STHQ/kilaueacove/tikinook/neopixel.py

# Adafruit NeoPixel library port to the rpi_ws281x library.
# Author: Tony DiCola (tony@tonydicola.com), Jeremy Garff (jer@jers.net)
import _rpi_ws281x as ws


def Color(red, green, blue):
    """Convert the provided red, green, blue color to a 24-bit color value.
    Each color component should be a value 0-255 where 0 is the lowest intensity
    and 255 is the highest intensity.
    """
    return (red << 16) | (green << 8) | blue


class _LED_Data(object):
    """Wrapper class which makes a SWIG LED color data array look and feel like
    a Python list of integers.
    """

    def __init__(self, channel, size):
        self.size = size
        self.channel = channel

    def __getitem__(self, pos):
        """Return the 24-bit RGB color value at the provided position or slice
        of positions.
        """
        # Handle if a slice of positions are passed in by grabbing all the values
        # and returning them in a list.
        if isinstance(pos, slice):
            return [ws.ws2811_led_get(self.channel, n) for n in range(pos.indices(self.size))]
        # Else assume the passed in value is a number to the position.
        else:
            return ws.ws2811_led_get(self.channel, pos)

    def __setitem__(self, pos, value):
        """Set the 24-bit RGB color value at the provided position or slice of
        positions.
        """
        # debug
        # print("pos: {}, value: {}", pos, value)
        # Handle if a slice of positions are passed in by setting the appropriate
        # LED data values to the provided values.
        if isinstance(pos, slice):
            index = 0
            for n in range(pos.indices(self.size)):
                ws.ws2811_led_set(self.channel, n, value[index])
                index += 1
        # Else assume the passed in value is a number to the position.
        else:
            # print("pos: {}, value: {}", type(pos), type(value))
            return ws.ws2811_led_set(self.channel, pos, value)
            # Testing value types:
            # print("type value.item(): {}", type(value.item()))
            # return ws.ws2811_led_set(self.channel, pos.item(), value.item())


class Adafruit_NeoPixel(object):
    def __init__(self, num, pin, freq_hz=800000, dma=5, invert=False, brightness=255, channel=0):
        """Class to represent a NeoPixel/WS281x LED display.  Num should be the
        number of pixels in the display, and pin should be the GPIO pin connected
        to the display signal line (must be a PWM pin like 18!).  Optional
        parameters are freq, the frequency of the display signal in hertz (default
        800khz), dma, the DMA channel to use (default 5), invert, a boolean
        specifying if the signal line should be inverted (default False), and
        channel, the PWM channel to use (defaults to 0).
        """
        # Create ws2811_t structure and fill in parameters.
        self._leds = ws.new_ws2811_t()

        # Initialize the channels to zero
        for channum in range(2):
            chan = ws.ws2811_channel_get(self._leds, channum)
            ws.ws2811_channel_t_count_set(chan, 0)
            ws.ws2811_channel_t_gpionum_set(chan, 0)
            ws.ws2811_channel_t_invert_set(chan, 0)
            ws.ws2811_channel_t_brightness_set(chan, 0)

        # Initialize the channel in use
        self._channel = ws.ws2811_channel_get(self._leds, channel)
        ws.ws2811_channel_t_count_set(self._channel, num)
        ws.ws2811_channel_t_gpionum_set(self._channel, pin)
        ws.ws2811_channel_t_invert_set(self._channel, 0 if not invert else 1)
        ws.ws2811_channel_t_brightness_set(self._channel, brightness)

        # Initialize the controller
        ws.ws2811_t_freq_set(self._leds, freq_hz)
        ws.ws2811_t_dmanum_set(self._leds, dma)

        # Grab the led data array.
        self._led_data = _LED_Data(self._channel, num)

    def __del__(self):
        # Clean up memory used by the library when not needed anymore.
        if self._leds is not None:
            ws.ws2811_fini(self._leds)
            ws.delete_ws2811_t(self._leds)
            self._leds = None
            self._channel = None
            # Note that ws2811_fini will free the memory used by led_data internally.

    def begin(self):
        """Initialize library, must be called once before other functions are
        called.
        """
        resp = ws.ws2811_init(self._leds)
        if resp != 0:
            raise RuntimeError('ws2811_init failed with code {0}'.format(resp))

    def show(self):
        """Update the display with the data from the LED buffer."""
        resp = ws.ws2811_render(self._leds)
        if resp != 0:
            raise RuntimeError('ws2811_render failed with code {0}'.format(resp))

    def setPixelColor(self, n, color):
        """Set LED at position n to the provided 24-bit color value (in RGB order).
        """
        # FIXME: I don't know what the hell is going on, but after I hooked
        # things back up on 2016-03-26, the NeoPixels are now displaying with 
        # R and G swapped. Temp fix here:
        red = (color >> 16) & 0xFF
        green = (color >> 8) & 0xFF
        blue = color & 0xFF
        color = (green << 16) | (red << 8) | blue

        # Now back to what it should be:
        self._led_data[n] = color

    def setPixelColorRGB(self, n, red, green, blue):
        """Set LED at position n to the provided red, green, and blue color.
        Each color component should be a value from 0 to 255 (where 0 is the
        lowest intensity and 255 is the highest intensity).
        """
        self.setPixelColor(n, Color(red, green, blue))

    def setBrightness(self, brightness):
        """Scale each LED in the buffer by the provided brightness.  A brightness
        of 0 is the darkest and 255 is the brightest.
        """
        ws.ws2811_channel_t_brightness_set(self._channel, brightness)

    def getPixels(self):
        """Return an object which allows access to the LED display data as if 
        it were a sequence of 24-bit RGB values.
        """
        return self._led_data

    def numPixels(self):
        """Return the number of pixels in the display."""
        return ws.ws2811_channel_t_count_get(self._channel)

    def getPixelColor(self, n):
        """Get the 24-bit RGB color value for the LED at position n."""
        return self._led_data[n]
